TechWizMichael/MCL-DSP8x8/PCB/DIYDSP_BB_ADAU1452v0.1/DIYDSP_BB_ADAU1452v0.1.kicad_pcb

## KiCad design PCB/DIYDSP_BB_ADAU1452v0.1/DIYDSP_BB_ADAU1452v0.1.kicad_pcb (2026-03-14)

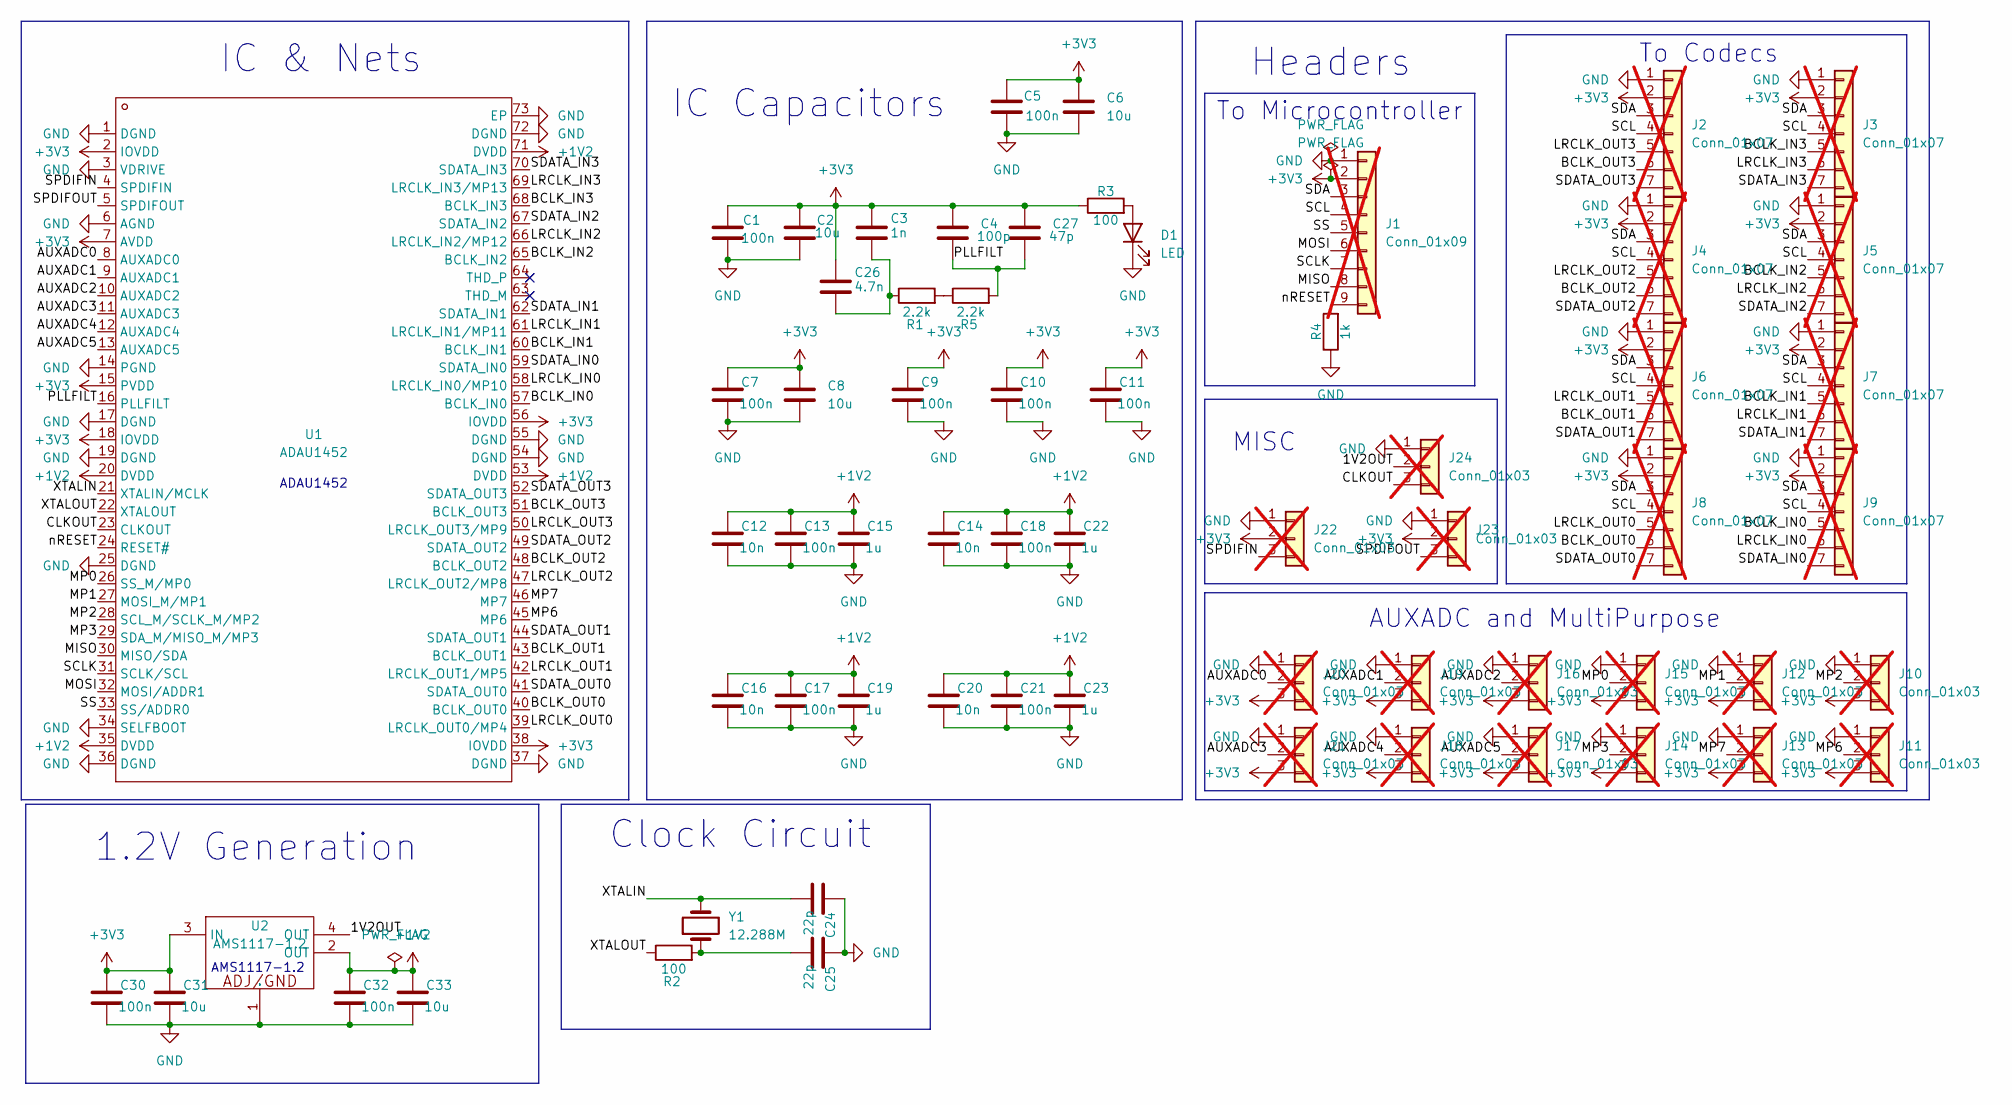
[picture p29: schematic DIYDSP_BB_ADAU1452v0.1.kicad_sch]

Parts:
C1, C5, C7, C9, C10, C11, C13, C17, C18, C21, C30, C32: 100n; C_0805_2012Metric; LCSC Part # C28233
C2, C6, C8, C31, C33: 10u; C_0805_2012Metric; LCSC Part # C15850
C3: 1n; C_0805_2012Metric; LCSC Part # C46653
C4: 100p; C_0805_2012Metric; LCSC Part # C1790
C12, C14, C16, C20: 10n; C_0805_2012Metric; LCSC Part # C1710
C15, C19, C22, C23: 1u; C_0805_2012Metric; LCSC Part # C28323
C24, C25: 22p; C_0805_2012Metric; LCSC Part # C1804
C26: 4.7n; C_0805_2012Metric; LCSC Part # C1744
C27: 47p; C_0805_2012Metric; LCSC Part # C14857
D1: LED; LED_0805_2012Metric; LCSC Part # C84256
J1: Conn_01x09; PinHeader_1x09_P2.54mm_Vertical; LCSC Part # C706881; not fitted
J2, J3, J4, J5, J6, J7, J8, J9: Conn_01x07; PinHeader_1x07_P2.54mm_Vertical; LCSC Part # C706879; not fitted
J10, J11, J12, J13, J14, J15, J16, J17, J18, J19, J20, J21, J22, J23, J24: Conn_01x03; PinHeader_1x03_P2.54mm_Vertical; LCSC Part # C19190477; not fitted
R1, R5: 2.2k; R_0805_2012Metric; LCSC Part # C17520
R2, R3: 100; R_0805_2012Metric; LCSC Part # C17408
R4: 1k; R_0805_2012Metric; LCSC Part # C17513
U1: ADAU1452; ADAU1452WBCPZ-RL; Manufacturer Part ADAU1452WBCPZ-RL; LCSC Part Name SigmaDSP 数字音频处理器
U2: AMS1117-1.2; Manufacturer Part AMS1117-1.2; LCSC Part Name 1.2V 1A 15V
Y1: 12.288M; Crystal_SMD_5032-2Pin_5.0x3.2mm; LCSC Part # C20624119

Connections:
+1V2: C12.1, C13.1, C14.1, C15.1, C16.1, C17.1, C18.1, C19.1, C20.1, C21.1, C22.1, C23.1, C32.1, C33.1, U1.20 (DVDD), U1.35 (DVDD), U1.53 (DVDD), U1.71 (DVDD), U2.2 (OUT)
+3V3: C1.1, C2.1, C3.1, C4.1, C5.1, C6.1, C7.1, C8.1, C9.1, C10.1, C11.1, C26.1, C27.1, C30.1, C31.1, J1.2, J2.2, J3.2, J4.2, J5.2, J6.2, J7.2, J8.2, J9.2, J10.3, J11.3, J12.3, J13.3, J14.3, J15.3, J16.3, J17.3, J18.3, J19.3, J20.3, J21.3, J22.2, J23.2, R3.1, U1.2 (IOVDD), U1.7 (AVDD), U1.15 (PVDD), U1.18 (IOVDD), U1.38 (IOVDD), U1.56 (IOVDD), U2.3 (IN)
/1V2OUT: J24.2, U2.4 (OUT)
/AUXADC0: J20.2, U1.8 (AUXADC0)
/AUXADC1: J19.2, U1.9 (AUXADC1)
/AUXADC2: J16.2, U1.10 (AUXADC2)
/AUXADC3: J21.2, U1.11 (AUXADC3)
/AUXADC4: J18.2, U1.12 (AUXADC4)
/AUXADC5: J17.2, U1.13 (AUXADC5)
/BCLK_IN0: J9.5, U1.57 (BCLK_IN0)
/BCLK_IN1: J7.5, U1.60 (BCLK_IN1)
/BCLK_IN2: J5.5, U1.65 (BCLK_IN2)
/BCLK_IN3: J3.5, U1.68 (BCLK_IN3)
/BCLK_OUT0: J8.6, U1.40 (BCLK_OUT0)
/BCLK_OUT1: J6.6, U1.43 (BCLK_OUT1)
/BCLK_OUT2: J4.6, U1.48 (BCLK_OUT2)
/BCLK_OUT3: J2.6, U1.51 (BCLK_OUT3)
/CLKOUT: J24.3, U1.23 (CLKOUT)
/LRCLK_IN0: J9.6, U1.58 (LRCLK_IN0/MP10)
/LRCLK_IN1: J7.6, U1.61 (LRCLK_IN1/MP11)
/LRCLK_IN2: J5.6, U1.66 (LRCLK_IN2/MP12)
/LRCLK_IN3: J3.6, U1.69 (LRCLK_IN3/MP13)
/LRCLK_OUT0: J8.5, U1.39 (LRCLK_OUT0/MP4)
/LRCLK_OUT1: J6.5, U1.42 (LRCLK_OUT1/MP5)
/LRCLK_OUT2: J4.5, U1.47 (LRCLK_OUT2/MP8)
/LRCLK_OUT3: J2.5, U1.50 (LRCLK_OUT3/MP9)
/MISO: J1.8, U1.30 (MISO/SDA)
/MOSI: J1.6, U1.32 (MOSI/ADDR1)
/MP0: J15.2, U1.26 (SS_M/MP0)
/MP1: J12.2, U1.27 (MOSI_M/MP1)
/MP2: J10.2, U1.28 (SCL_M/SCLK_M/MP2)
/MP3: J14.2, U1.29 (SDA_M/MISO_M/MP3)
/MP6: J11.2, U1.45 (MP6)
/MP7: J13.2, U1.46 (MP7)
/PLLFILT: C4.2, C27.2, R5.2, U1.16 (PLLFILT)
/SCL: J1.4, J2.4, J3.4, J4.4, J5.4, J6.4, J7.4, J8.4, J9.4
/SCLK: J1.7, U1.31 (SCLK/SCL)
/SDA: J1.3, J2.3, J3.3, J4.3, J5.3, J6.3, J7.3, J8.3, J9.3
/SDATA_IN0: J9.7, U1.59 (SDATA_IN0)
/SDATA_IN1: J7.7, U1.62 (SDATA_IN1)
/SDATA_IN2: J5.7, U1.67 (SDATA_IN2)
/SDATA_IN3: J3.7, U1.70 (SDATA_IN3)
/SDATA_OUT0: J8.7, U1.41 (SDATA_OUT0)
/SDATA_OUT1: J6.7, U1.44 (SDATA_OUT1)
/SDATA_OUT2: J4.7, U1.49 (SDATA_OUT2)
/SDATA_OUT3: J2.7, U1.52 (SDATA_OUT3)
/SPDIFIN: J22.3, U1.4 (SPDIFIN)
/SPDIFOUT: J23.3, U1.5 (SPDIFOUT)
/SS: J1.5, U1.33 (SS/ADDR0)
/XTALIN: C24.2, U1.21 (XTALIN/MCLK), Y1.2
/XTALOUT: R2.1, U1.22 (XTALOUT)
/nRESET: J1.9, R4.2, U1.24 (RESET#)
GND: C1.2, C2.2, C5.2, C6.2, C7.2, C8.2, C9.2, C10.2, C11.2, C12.2, C13.2, C14.2, C15.2, C16.2, C17.2, C18.2, C19.2, C20.2, C21.2, C22.2, C23.2, C24.1, C25.1, C30.2, C31.2, C32.2, C33.2, D1.1 (K), J1.1, J2.1, J3.1, J4.1, J5.1, J6.1, J7.1, J8.1, J9.1, J10.1, J11.1, J12.1, J13.1, J14.1, J15.1, J16.1, J17.1, J18.1, J19.1, J20.1, J21.1, J22.1, J23.1, J24.1, R4.1, U1.1 (DGND), U1.3 (VDRIVE), U1.6 (AGND), U1.14 (PGND), U1.17 (DGND), U1.19 (DGND), U1.25 (DGND), U1.34 (SELFBOOT), U1.36 (DGND), U1.37 (DGND), U1.54 (DGND), U1.55 (DGND), U1.72 (DGND), U1.73 (EP), U2.1 (ADJ/GND)
unnamed: C25.2, R2.2, Y1.1
unnamed: C3.2, C26.2, R1.1
unnamed: D1.2 (A), R3.2
unnamed: R1.2, R5.1

Notes on the sheet:
To Microcontroller
IC & Nets
IC Capacitors
MISC
Headers
1.2V Generation
AMS1117-1.2
ADAU1452
To Codecs
AUXADC and MultiPurpose
Clock Circuit

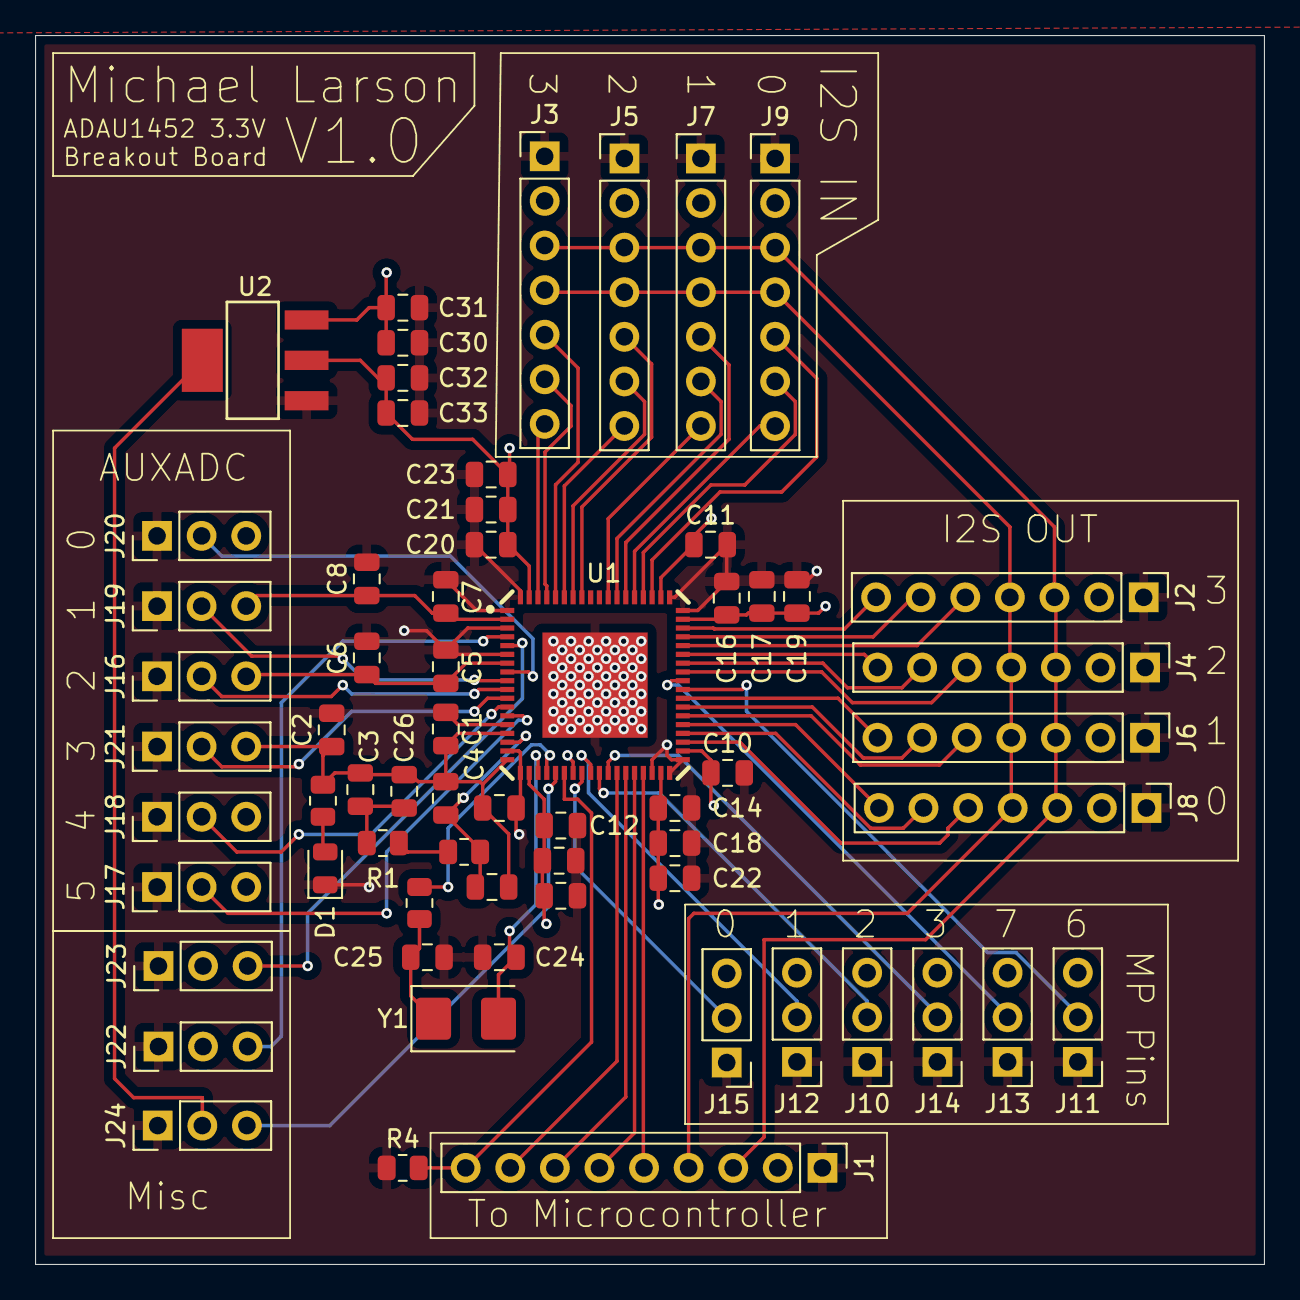
[picture p30: board DIYDSP_BB_ADAU1452v0.1.kicad_pcb from above]

Board: 4 copper layers, 70.0 x 70.0 mm, 64 parts (0 on the bottom side), 57 nets.
