TechWizMichael/MCL-DSP8x8/Firmware/MCL-DSP8x8/ADAU1452/MCL-DSP8x8Test_IC_1_PARAM.h

/*
 * File:           C:\Users\loral\OneDrive\Documents\EE4893\MCL-DSP8x8\Firmware\MCL-DSP8x8\ADAU1452\MCL-DSP8x8Test_IC_1_PARAM.h
 *
 * Created:        Wednesday, July 1, 2026 12:42:35 AM
 * Description:    MCL-DSP8x8Test:IC 1 parameter RAM definitions.
 *
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
 * This software may only be used to program products purchased from
 * Analog Devices for incorporation by you into audio products that
 * are intended for resale to audio product end users. This software
 * may not be distributed whole or in any part to third parties.
 *
 * Copyright ©2026 Analog Devices, Inc. All rights reserved.
 */
#ifndef __MCL_DSP8X8TEST_IC_1_PARAM_H__
#define __MCL_DSP8X8TEST_IC_1_PARAM_H__


/* Module SafeLoadModule - SafeLoadModule*/
#define MOD_SAFELOADMODULE_COUNT                       10
#define MOD_SAFELOADMODULE_DEVICE                      "IC1"
#define MOD_SAFELOADMODULE_DATA_SAFELOAD0_ADDR         24576
#define MOD_SAFELOADMODULE_DATA_SAFELOAD1_ADDR         24577
#define MOD_SAFELOADMODULE_DATA_SAFELOAD2_ADDR         24578
#define MOD_SAFELOADMODULE_DATA_SAFELOAD3_ADDR         24579
#define MOD_SAFELOADMODULE_DATA_SAFELOAD4_ADDR         24580
#define MOD_SAFELOADMODULE_ADDRESS_SAFELOAD_ADDR       24581
#define MOD_SAFELOADMODULE_NUM_SAFELOAD_ADDR           24582

/* Module Heartbeat_Pulse - Pulse with dynamic duty cycle*/
#define MOD_LED_HEARTBEAT_HEARTBEAT_PULSE_COUNT        4
#define MOD_LED_HEARTBEAT_HEARTBEAT_PULSE_DEVICE       "IC1"
#define MOD_LED_HEARTBEAT_HEARTBEAT_PULSE_ALG0_ISROUNDED_ADDR 20
#define MOD_LED_HEARTBEAT_HEARTBEAT_PULSE_ALG0_ISROUNDED_VALUE SIGMASTUDIOTYPE_8_24_CONVERT(0)
#define MOD_LED_HEARTBEAT_HEARTBEAT_PULSE_ALG0_ISROUNDED_TYPE SIGMASTUDIOTYPE_8_24
#define MOD_LED_HEARTBEAT_HEARTBEAT_PULSE_ALG0_FREQ_STEP_ADDR 21
#define MOD_LED_HEARTBEAT_HEARTBEAT_PULSE_ALG0_FREQ_STEP_VALUE SIGMASTUDIOTYPE_8_24_CONVERT(4.16666666666667E-05)
#define MOD_LED_HEARTBEAT_HEARTBEAT_PULSE_ALG0_FREQ_STEP_TYPE SIGMASTUDIOTYPE_8_24
#define MOD_LED_HEARTBEAT_HEARTBEAT_PULSE_ALG0_ON_ADDR 22
#define MOD_LED_HEARTBEAT_HEARTBEAT_PULSE_ALG0_ON_VALUE SIGMASTUDIOTYPE_8_24_CONVERT(1)
#define MOD_LED_HEARTBEAT_HEARTBEAT_PULSE_ALG0_ON_TYPE SIGMASTUDIOTYPE_8_24
#define MOD_LED_HEARTBEAT_HEARTBEAT_PULSE_ALG0_TH_ADDR 23
#define MOD_LED_HEARTBEAT_HEARTBEAT_PULSE_ALG0_TH_VALUE SIGMASTUDIOTYPE_8_24_CONVERT(0.5)
#define MOD_LED_HEARTBEAT_HEARTBEAT_PULSE_ALG0_TH_TYPE SIGMASTUDIOTYPE_8_24

/* Module Tone_Gen - Sine Tone with Phase and Gain*/
#define MOD_TONE_GEN_COUNT                             4
#define MOD_TONE_GEN_DEVICE                            "IC1"
#define MOD_TONE_GEN_ALG0_SINEPHASEGAINALGS3002GAIN00_ADDR 24
#define MOD_TONE_GEN_ALG0_SINEPHASEGAINALGS3002GAIN00_VALUE SIGMASTUDIOTYPE_8_24_CONVERT(3.98107170553497)
#define MOD_TONE_GEN_ALG0_SINEPHASEGAINALGS3002GAIN00_TYPE SIGMASTUDIOTYPE_8_24
#define MOD_TONE_GEN_ALG0_SINEPHASEGAINALGS3002INDEXFPHI00_ADDR 25
#define MOD_TONE_GEN_ALG0_SINEPHASEGAINALGS3002INDEXFPHI00_FIXPT 0x00000000
#define MOD_TONE_GEN_ALG0_SINEPHASEGAINALGS3002INDEXFPHI00_VALUE SIGMASTUDIOTYPE_INTEGER_CONVERT(0)
#define MOD_TONE_GEN_ALG0_SINEPHASEGAINALGS3002INDEXFPHI00_TYPE SIGMASTUDIOTYPE_INTEGER
#define MOD_TONE_GEN_ALG0_SINEPHASEGAINALGS3002INDEXFPHI01_ADDR 26
#define MOD_TONE_GEN_ALG0_SINEPHASEGAINALGS3002INDEXFPHI01_FIXPT 0x00000000
#define MOD_TONE_GEN_ALG0_SINEPHASEGAINALGS3002INDEXFPHI01_VALUE SIGMASTUDIOTYPE_INTEGER_CONVERT(0)
#define MOD_TONE_GEN_ALG0_SINEPHASEGAINALGS3002INDEXFPHI01_TYPE SIGMASTUDIOTYPE_INTEGER
#define MOD_TONE_GEN_ALG0_INCREMENT_ADDR               29
#define MOD_TONE_GEN_ALG0_INCREMENT_VALUE              SIGMASTUDIOTYPE_8_24_CONVERT(0.0025)
#define MOD_TONE_GEN_ALG0_INCREMENT_TYPE               SIGMASTUDIOTYPE_8_24

/* Module Noise_Pink_Filter - Pinking*/
#define MOD_NOISE_PINK_FILTER_COUNT                    16
#define MOD_NOISE_PINK_FILTER_DEVICE                   "IC1"
#define MOD_NOISE_PINK_FILTER_ALG0_PINKFALGS3001INPUTGAIN_ADDR 34
#define MOD_NOISE_PINK_FILTER_ALG0_PINKFALGS3001INPUTGAIN_VALUE SIGMASTUDIOTYPE_8_24_CONVERT(1)
#define MOD_NOISE_PINK_FILTER_ALG0_PINKFALGS3001INPUTGAIN_TYPE SIGMASTUDIOTYPE_8_24
#define MOD_NOISE_PINK_FILTER_ALG0_PINKFALGS3001OUTPUTGAIN_ADDR 35
#define MOD_NOISE_PINK_FILTER_ALG0_PINKFALGS3001OUTPUTGAIN_VALUE SIGMASTUDIOTYPE_8_24_CONVERT(1)
#define MOD_NOISE_PINK_FILTER_ALG0_PINKFALGS3001OUTPUTGAIN_TYPE SIGMASTUDIOTYPE_8_24
#define MOD_NOISE_PINK_FILTER_ALG0_PINKFALGS3001COEFF0A0_ADDR 36
#define MOD_NOISE_PINK_FILTER_ALG0_PINKFALGS3001COEFF0A0_VALUE SIGMASTUDIOTYPE_8_24_CONVERT(0.99886)
#define MOD_NOISE_PINK_FILTER_ALG0_PINKFALGS3001COEFF0A0_TYPE SIGMASTUDIOTYPE_8_24
#define MOD_NOISE_PINK_FILTER_ALG0_PINKFALGS3001COEFF0A1_ADDR 37
#define MOD_NOISE_PINK_FILTER_ALG0_PINKFALGS3001COEFF0A1_VALUE SIGMASTUDIOTYPE_8_24_CONVERT(0.0555179)
#define MOD_NOISE_PINK_FILTER_ALG0_PINKFALGS3001COEFF0A1_TYPE SIGMASTUDIOTYPE_8_24
#define MOD_NOISE_PINK_FILTER_ALG0_PINKFALGS3001COEFF0A2_ADDR 38
#define MOD_NOISE_PINK_FILTER_ALG0_PINKFALGS3001COEFF0A2_VALUE SIGMASTUDIOTYPE_8_24_CONVERT(0.99332)
#define MOD_NOISE_PINK_FILTER_ALG0_PINKFALGS3001COEFF0A2_TYPE SIGMASTUDIOTYPE_8_24
#define MOD_NOISE_PINK_FILTER_ALG0_PINKFALGS3001COEFF0A3_ADDR 39
#define MOD_NOISE_PINK_FILTER_ALG0_PINKFALGS3001COEFF0A3_VALUE SIGMASTUDIOTYPE_8_24_CONVERT(0.0750759)
#define MOD_NOISE_PINK_FILTER_ALG0_PINKFALGS3001COEFF0A3_TYPE SIGMASTUDIOTYPE_8_24
#define MOD_NOISE_PINK_FILTER_ALG0_PINKFALGS3001COEFF0A4_ADDR 40
#define MOD_NOISE_PINK_FILTER_ALG0_PINKFALGS3001COEFF0A4_VALUE SIGMASTUDIOTYPE_8_24_CONVERT(0.969)
#define MOD_NOISE_PINK_FILTER_ALG0_PINKFALGS3001COEFF0A4_TYPE SIGMASTUDIOTYPE_8_24
#define MOD_NOISE_PINK_FILTER_ALG0_PINKFALGS3001COEFF0A5_ADDR 41
#define MOD_NOISE_PINK_FILTER_ALG0_PINKFALGS3001COEFF0A5_VALUE SIGMASTUDIOTYPE_8_24_CONVERT(0.153852)
#define MOD_NOISE_PINK_FILTER_ALG0_PINKFALGS3001COEFF0A5_TYPE SIGMASTUDIOTYPE_8_24
#define MOD_NOISE_PINK_FILTER_ALG0_PINKFALGS3001COEFF0A6_ADDR 42
#define MOD_NOISE_PINK_FILTER_ALG0_PINKFALGS3001COEFF0A6_VALUE SIGMASTUDIOTYPE_8_24_CONVERT(0.8665)
#define MOD_NOISE_PINK_FILTER_ALG0_PINKFALGS3001COEFF0A6_TYPE SIGMASTUDIOTYPE_8_24
#define MOD_NOISE_PINK_FILTER_ALG0_PINKFALGS3001COEFF0A7_ADDR 43
#define MOD_NOISE_PINK_FILTER_ALG0_PINKFALGS3001COEFF0A7_VALUE SIGMASTUDIOTYPE_8_24_CONVERT(0.3104856)
#define MOD_NOISE_PINK_FILTER_ALG0_PINKFALGS3001COEFF0A7_TYPE SIGMASTUDIOTYPE_8_24
#define MOD_NOISE_PINK_FILTER_ALG0_PINKFALGS3001COEFF0A8_ADDR 44
#define MOD_NOISE_PINK_FILTER_ALG0_PINKFALGS3001COEFF0A8_VALUE SIGMASTUDIOTYPE_8_24_CONVERT(0.55)
#define MOD_NOISE_PINK_FILTER_ALG0_PINKFALGS3001COEFF0A8_TYPE SIGMASTUDIOTYPE_8_24
#define MOD_NOISE_PINK_FILTER_ALG0_PINKFALGS3001COEFF0A9_ADDR 45
#define MOD_NOISE_PINK_FILTER_ALG0_PINKFALGS3001COEFF0A9_VALUE SIGMASTUDIOTYPE_8_24_CONVERT(0.5329522)
#define MOD_NOISE_PINK_FILTER_ALG0_PINKFALGS3001COEFF0A9_TYPE SIGMASTUDIOTYPE_8_24
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
#define MOD_MIXER_ALG0_AUDIOSIGNALROUTER34S300ALG1ALPHA1_ADDR 149
#define MOD_MIXER_ALG0_AUDIOSIGNALROUTER34S300ALG1ALPHA1_VALUE SIGMASTUDIOTYPE_8_24_CONVERT(0.000254280816193386)
#define MOD_MIXER_ALG0_AUDIOSIGNALROUTER34S300ALG1ALPHA1_TYPE SIGMASTUDIOTYPE_8_24

/* Module Master_Gain - Gain*/
#define MOD_MASTER_GAIN_COUNT                          2
#define MOD_MASTER_GAIN_DEVICE                         "IC1"
#define MOD_MASTER_GAIN_ALG0_TARGET_ADDR               151
#define MOD_MASTER_GAIN_ALG0_TARGET_VALUE              SIGMASTUDIOTYPE_8_24_CONVERT(1)
#define MOD_MASTER_GAIN_ALG0_TARGET_TYPE               SIGMASTUDIOTYPE_8_24
#define MOD_MASTER_GAIN_ALG0_SLEW_MODE_ADDR            152
#define MOD_MASTER_GAIN_ALG0_SLEW_MODE_FIXPT           0x0000208A
#define MOD_MASTER_GAIN_ALG0_SLEW_MODE_VALUE           SIGMASTUDIOTYPE_INTEGER_CONVERT(8330)
#define MOD_MASTER_GAIN_ALG0_SLEW_MODE_TYPE            SIGMASTUDIOTYPE_INTEGER

/* Module Heartbeat_DC - DC Input Entry*/
#define MOD_LED_HEARTBEAT_HEARTBEAT_DC_COUNT           1
#define MOD_LED_HEARTBEAT_HEARTBEAT_DC_DEVICE          "IC1"
#define MOD_LED_HEARTBEAT_HEARTBEAT_DC_DCINPALG145X1VALUE_ADDR 153
#define MOD_LED_HEARTBEAT_HEARTBEAT_DC_DCINPALG145X1VALUE_VALUE SIGMASTUDIOTYPE_8_24_CONVERT(0)
#define MOD_LED_HEARTBEAT_HEARTBEAT_DC_DCINPALG145X1VALUE_TYPE SIGMASTUDIOTYPE_8_24

/* Module Noise_Gen - White Noise*/
#define MOD_NOISE_GEN_COUNT                            1
#define MOD_NOISE_GEN_DEVICE                           "IC1"
#define MOD_NOISE_GEN_ENABLENOISE_ADDR                 154
#define MOD_NOISE_GEN_ENABLENOISE_VALUE                SIGMASTUDIOTYPE_8_24_CONVERT(0)
#define MOD_NOISE_GEN_ENABLENOISE_TYPE                 SIGMASTUDIOTYPE_8_24

/* Module Heartbeat_Switch - Mono Switch Nx1*/
#define MOD_LED_HEARTBEAT_HEARTBEAT_SWITCH_COUNT       1
#define MOD_LED_HEARTBEAT_HEARTBEAT_SWITCH_DEVICE      "IC1"
#define MOD_LED_HEARTBEAT_HEARTBEAT_SWITCH_MONOMUXSIGMA300NS1INDEX_ADDR 155
#define MOD_LED_HEARTBEAT_HEARTBEAT_SWITCH_MONOMUXSIGMA300NS1INDEX_FIXPT 0x00000000
#define MOD_LED_HEARTBEAT_HEARTBEAT_SWITCH_MONOMUXSIGMA300NS1INDEX_VALUE SIGMASTUDIOTYPE_INTEGER_CONVERT(0)
#define MOD_LED_HEARTBEAT_HEARTBEAT_SWITCH_MONOMUXSIGMA300NS1INDEX_TYPE SIGMASTUDIOTYPE_INTEGER

#endif
